PaoloJN/openchess/docs/images/system-overview.html

# OpenChess — System Overview · bottom view

rev 0.2 · 2026-06-05 · per DESIGN_NOTES.md

Controller PCB — ESP32 brain

M1 · Lipo Rider Plus — power module

LiPo battery — 1S protected, 1500 mAh

User UI panel — OLED, buttons, USB-C

Matrix PCB — back face shown
