PaoloJN/openchess/docs/archive/legacy-notes.md

Here’s what I’m thinking for the PCB layout:

On the front side of the PCB, we should keep only the components that need to interact directly with the chessboard surface, mainly the LEDs and hall sensors. If any small capacitors or resistors absolutely need to be placed on the front for routing, signal integrity, or electrical reasons, that’s fine, but ideally the front should stay as clean and simple as possible.

On the back side of the PCB, we can place most of the main electronics to keep the top side clean. This would include the ESP32, transistors, ICs, support components, connectors, and anything else that does not need to be on the front side.

I’d also like the back side components to be neatly grouped and organized, instead of scattered randomly. The placement should still take into consideration important PCB design details such as signal routing, trace length, power distribution, grounding, noise, heat, and ease of assembly/debugging. So the goal is not just to make it look clean, but also to make sure the layout is electrically sound and practical.

For the user facing components, like the battery LED, power switch, charging port, or any external controls, I’d prefer not to place them on the top face of the chessboard. Instead, I want them mounted on the side of the wooden chessboard enclosure. We can run wires, a small cable, or a small strip/connector from the bottom side of the PCB to those side mounted components.

Ideally, these user facing components should be grouped together neatly on the bottom left side of the wooden board, so everything is easy to access but still looks clean.

Does this layout approach make sense? If you have a better recommendation for component placement, routing, or how to handle the side mounted controls, let me know and we can iterate from there.

---

I like the overall plan. I just have a few changes:

1. User-facing component cluster

For the user-facing components, I’d prefer to connect them using cables/wires instead of fixed PCB cutouts. This gives more flexibility during assembly and makes it easier to mount those components cleanly and flush with the side of the wooden board.

2. Grid placement script

Instead of keeping the current grid_placement.py, move it into:

scripts/archived/grid_placement.py

Then create a clean new version that matches the structure and style. Feel free to split it into multiple scripts or group related logic together, as long as each script has a clear specific purpose.

3. Future reusability

I also want the placement scripts to be reusable when the schematic changes in the future. After I clean up or modify the schematic, I should be able to update and rerun the scripts to generate a clean PCB layout again.

---

Sheet naming convention after Phase C, matching the existing PCB-layout
scripts:

┌────────────────────────────┬─────────────────────────────────────────────┐
│ New file │ Contains │
├────────────────────────────┼─────────────────────────────────────────────┤
│ openchess.kicad_sch │ Root — 5 sheet symbols, title block, │
│ │ PWR_FLAGs │
├────────────────────────────┼─────────────────────────────────────────────┤
│ │ USB-C J1, MT3608 J2, SW1, TP4056 net, │
│ 01_power.kicad_sch │ MT3608 boost, level shifter U67, bulk caps │
│ │ C5–C8, BATT_LED1 │
├────────────────────────────┼─────────────────────────────────────────────┤
│ 02_controller.kicad_sch │ ESP32 U1, C2 (EN cap), strap pulls, │
│ │ USB-serial pads │
├────────────────────────────┼─────────────────────────────────────────────┤
│ 03_column_driver.kicad_sch │ 74HC595 U2, Q1–Q8 (2N3906), base resistors, │
│ │ row pull-ups │
├────────────────────────────┼─────────────────────────────────────────────┤
│ 04_hall_matrix.kicad_sch │ 64× A3144 (U3..U66), 8×8 grid layout │
│ │ matching U(3 + file\*8 + rank) │
├────────────────────────────┼─────────────────────────────────────────────┤
│ 05_led_chain.kicad_sch │ RENAMED from led_chain.kicad_sch — 81× │
│ │ WS2812 + decoupling, per-row power rails │
└────────────────────────────┴─────────────────────────────────────────────┘
